dr3y/BioPick/images/colony_picker.png

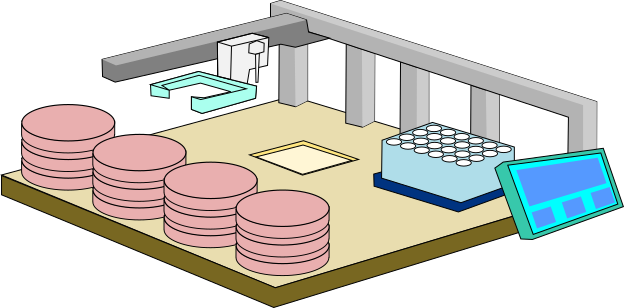
images/colony_picker.png
