dr3y/BioPick/images/IMG_20200820_125340495.jpg

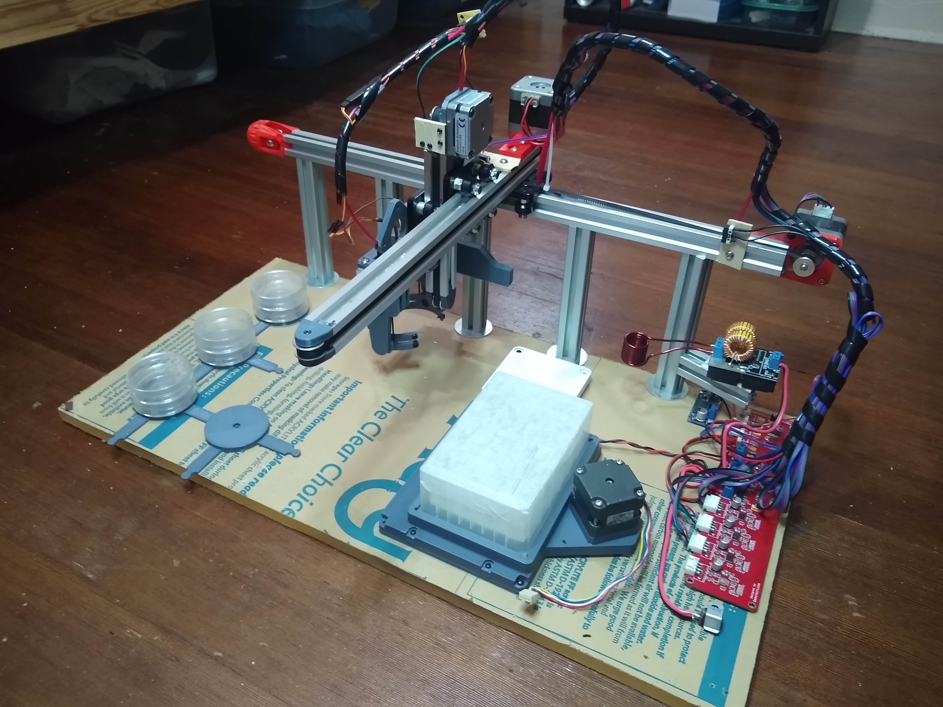
images/IMG_20200820_125340495.jpg
