dr3y/BioPick/software/raspberry_pi/pictures/A1_calib.png

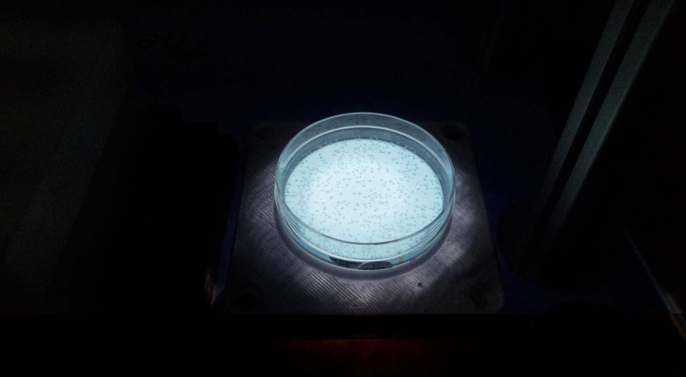
software/raspberry_pi/pictures/A1_calib.png
