dr3y/BioPick/physical/stl/plate_shaker/driver_pulley.stl

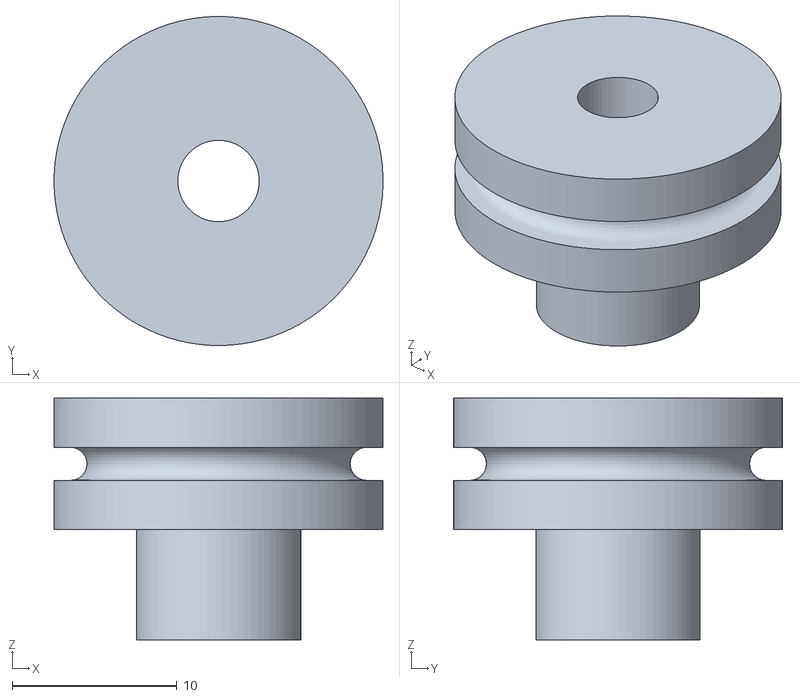
[picture p21: CAD file, 2020-08-20]
physical/stl/plate_shaker/driver_pulley.stl
20.0 x 20.0 x 14.7
