dr3y/BioPick/physical/stl/frame/idle_holder2.stl

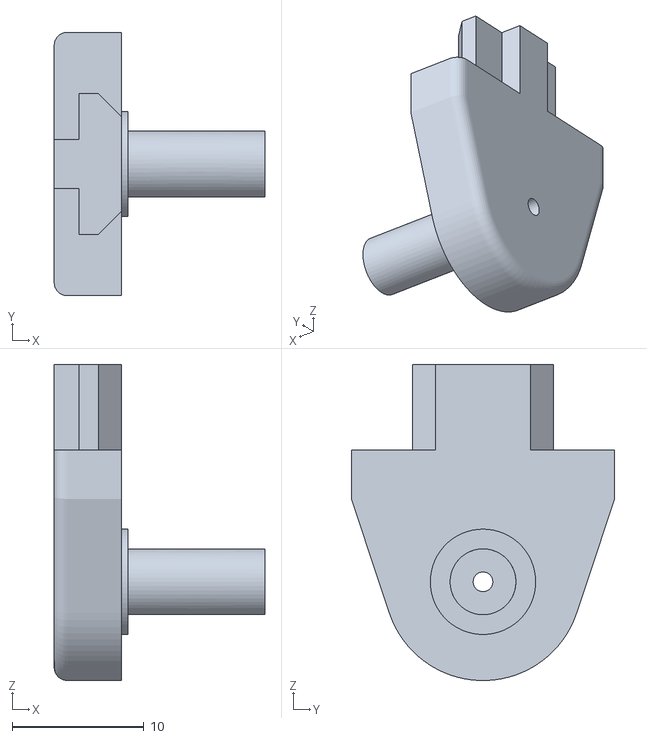
[picture p22: CAD file, 2020-08-20]
physical/stl/frame/idle_holder2.stl
16.0 x 20.0 x 24.0
