dr3y/BioPick/physical/stl/gripper/outershaft_bigger.stl

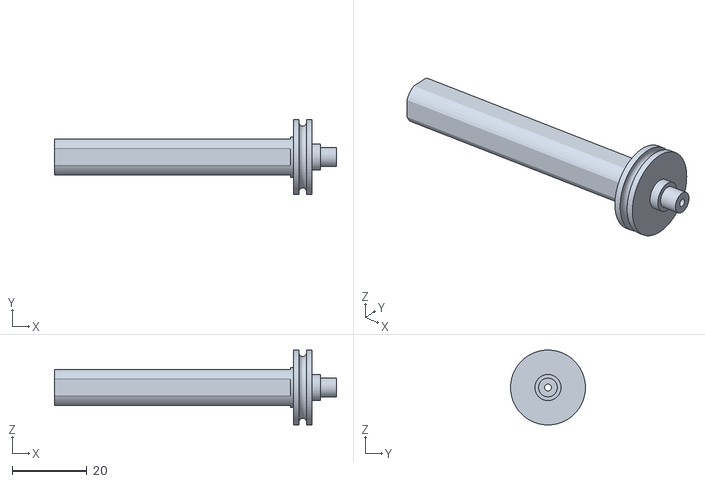
[picture p23: CAD file, 2020-08-20]
physical/stl/gripper/outershaft_bigger.stl
75.2 x 20.0 x 20.0
