dr3y/BioPick/physical/stl/plate_shaker/top_stator.stl

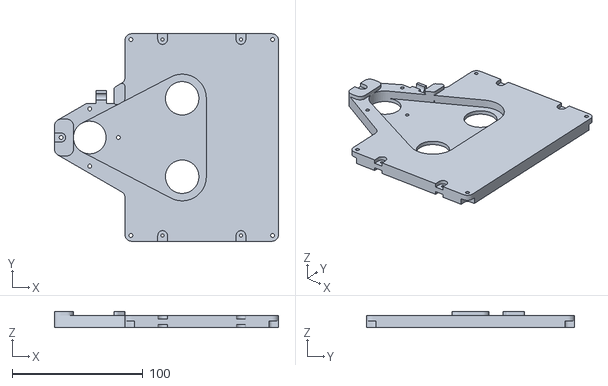
[picture p24: CAD file, 2020-08-20]
physical/stl/plate_shaker/top_stator.stl
171.5 x 159.0 x 12.5
