dr3y/BioPick/physical/stl/frame/motorholder.stl

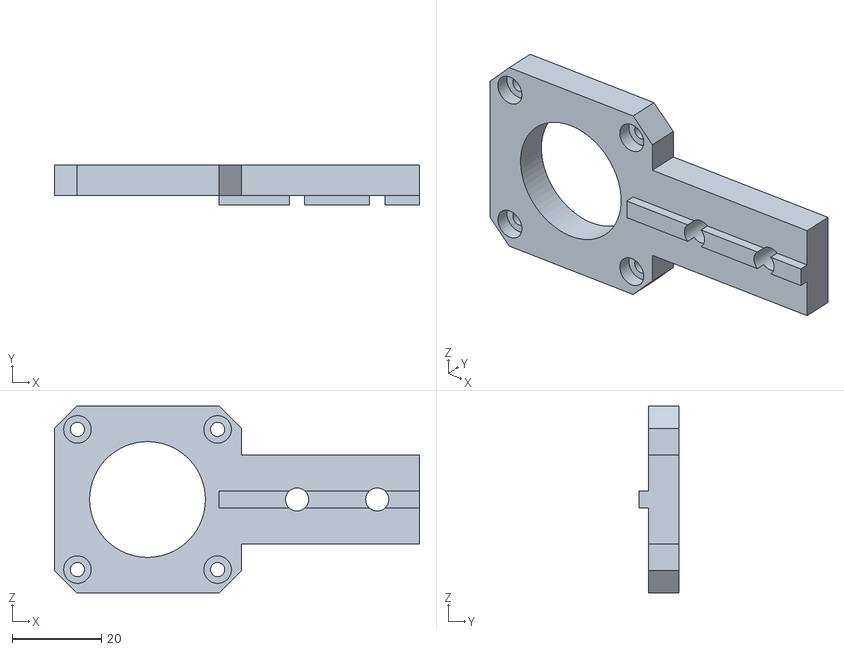
[picture p25: CAD file, 2020-08-20]
physical/stl/frame/motorholder.stl
82.0 x 9.00 x 42.0
