dr3y/BioPick/physical/stl/gripper/bearing cover.stl

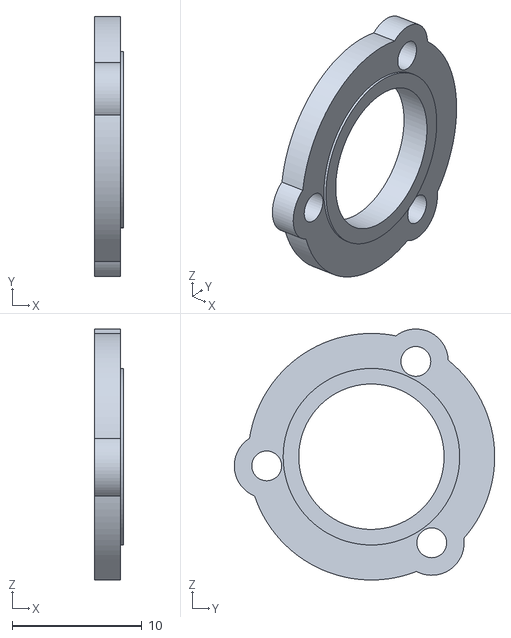
[picture p26: CAD file, 2020-08-20]
physical/stl/gripper/bearing cover.stl
2.20 x 20.1 x 19.3
