dr3y/BioPick/physical/stl/plate_shaker/rotor_pulley.stl

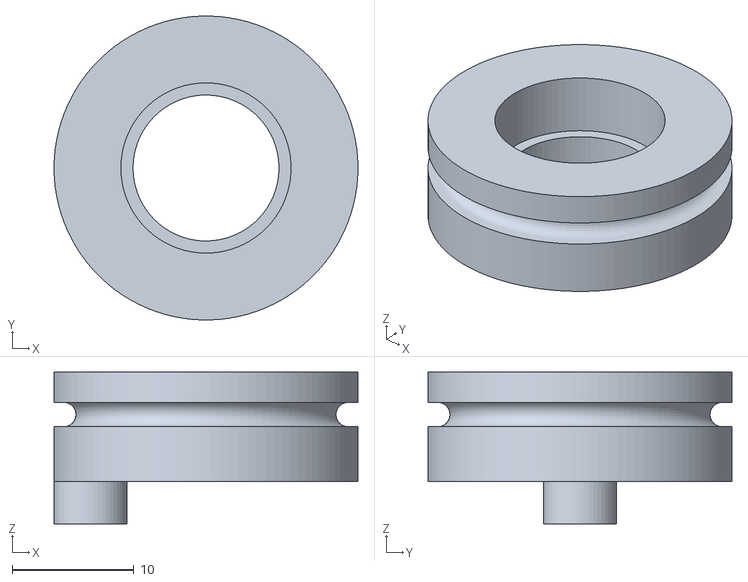
[picture p27: CAD file, 2020-08-20]
physical/stl/plate_shaker/rotor_pulley.stl
25.0 x 25.0 x 12.5
