dr3y/BioPick/physical/stl/frame/gripmount.stl

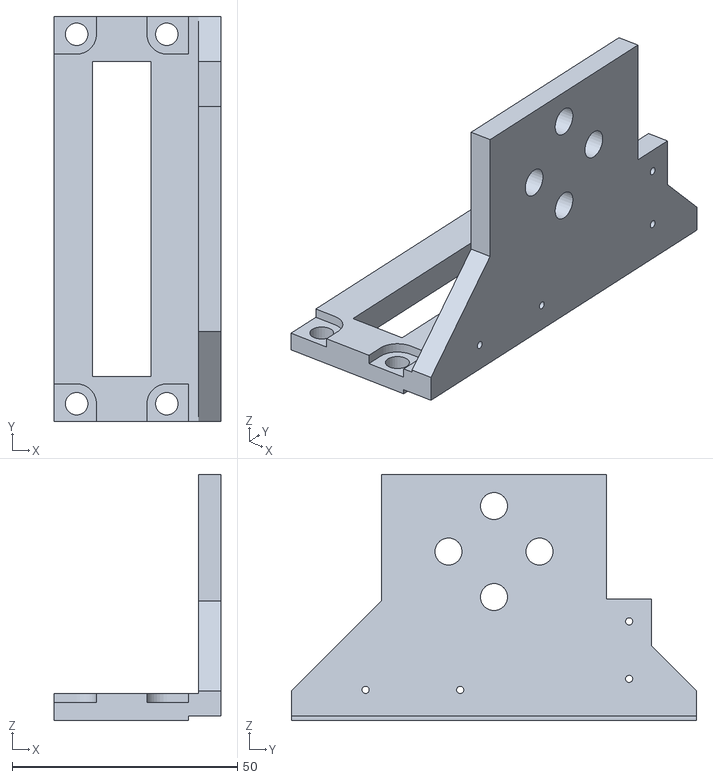
[picture p28: CAD file, 2020-08-20]
physical/stl/frame/gripmount.stl
37.0 x 90.0 x 54.6
