dr3y/BioPick/physical/stl/frame/y_clamp.stl

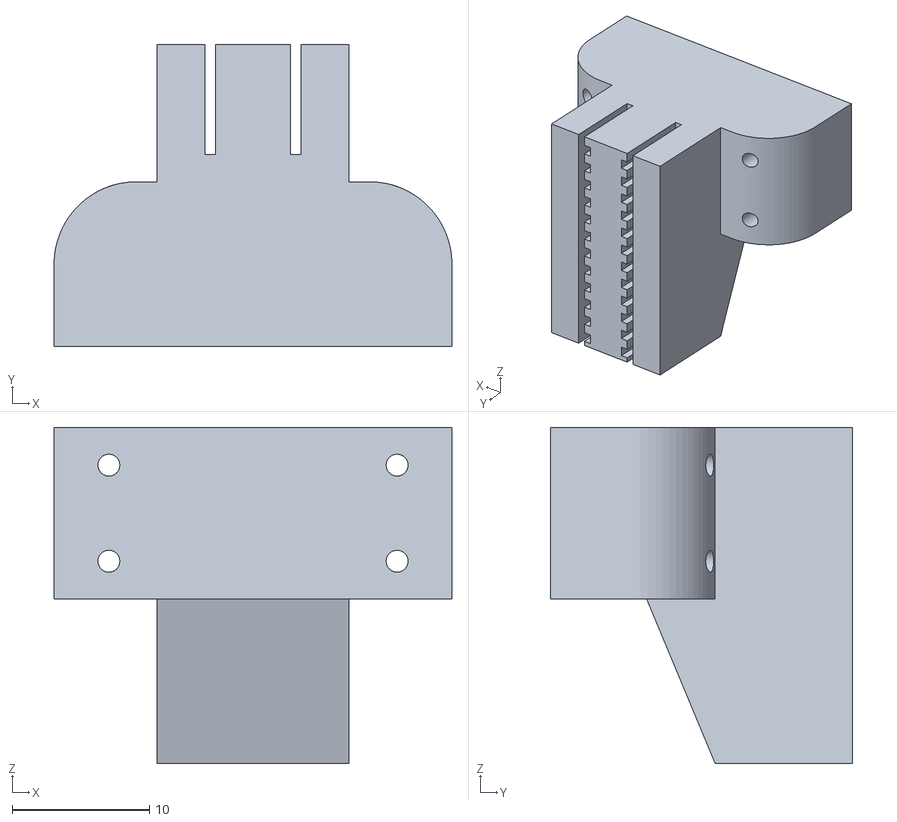
[picture p30: CAD file, 2020-08-20]
physical/stl/frame/y_clamp.stl
29.0 x 22.0 x 24.5
