dr3y/BioPick/physical/stl/gripper/largebevelgear.stl

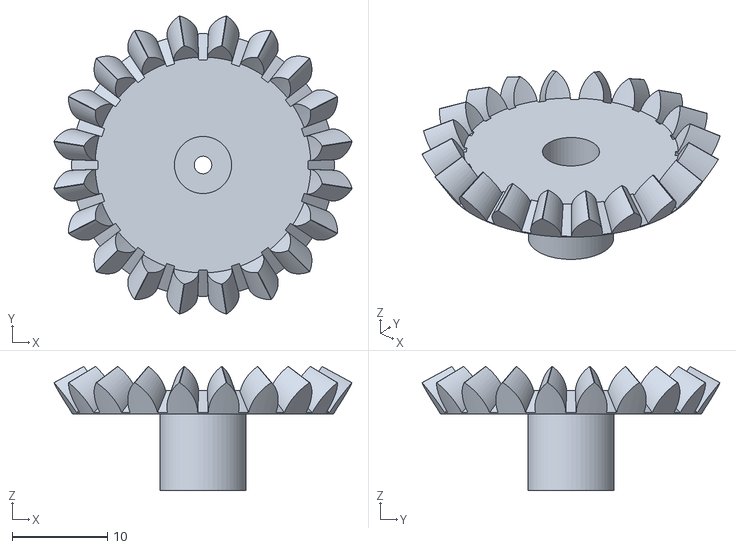
[picture p31: CAD file, 2020-08-20]
physical/stl/gripper/largebevelgear.stl
31.3 x 31.3 x 13.0
