dr3y/BioPick/physical/stl/plate_shaker/motor_spacer.stl

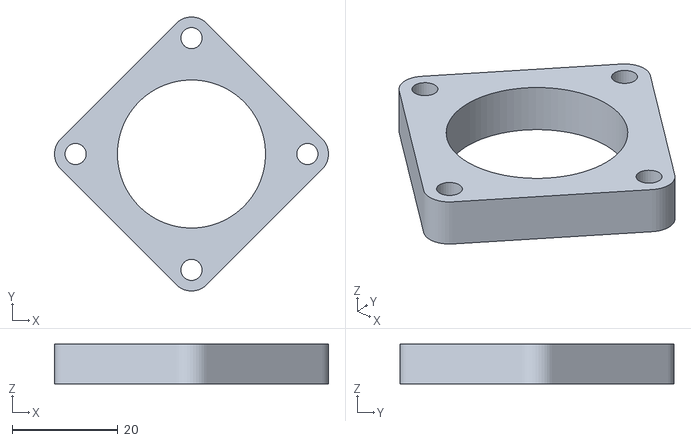
[picture p32: CAD file, 2020-08-20]
physical/stl/plate_shaker/motor_spacer.stl
51.8 x 51.8 x 7.50
