dr3y/BioPick/physical/stl/gripper/hand.stl

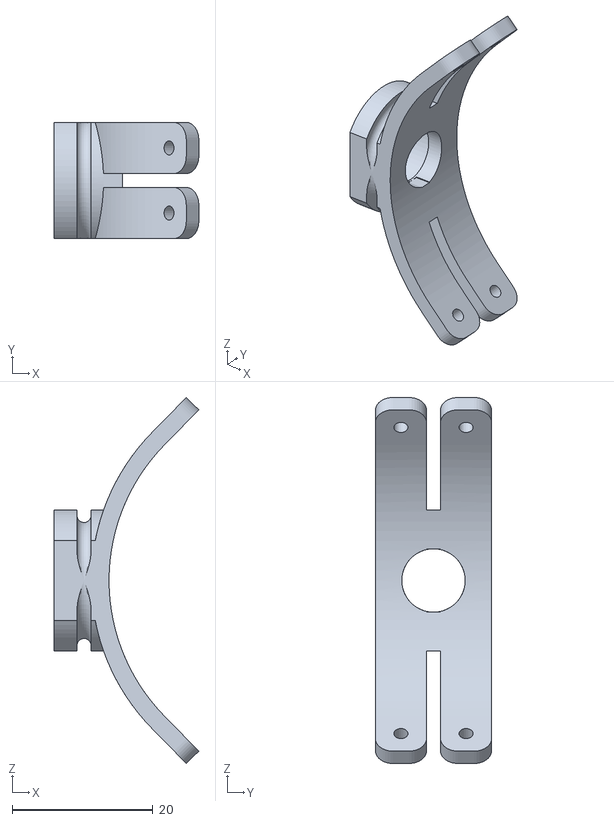
[picture p33: CAD file, 2020-08-20]
physical/stl/gripper/hand.stl
20.6 x 16.5 x 52.0
