dr3y/BioPick/physical/stl/gripper/bevelmount_biggerhole.stl

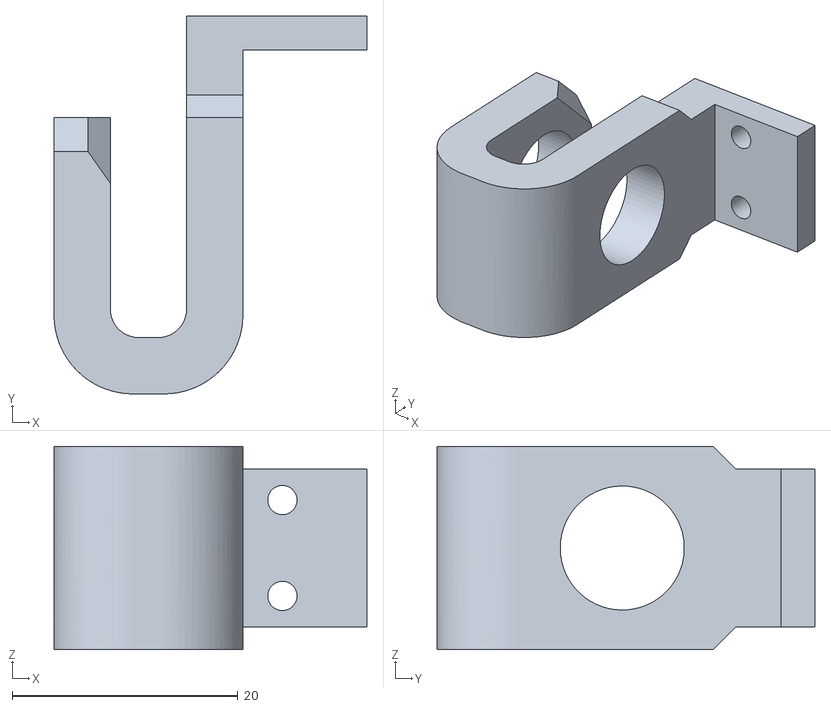
[picture p34: CAD file, 2020-08-20]
physical/stl/gripper/bevelmount_biggerhole.stl
27.8 x 33.5 x 18.0
