dr3y/BioPick/physical/stl/gripper/arm.stl

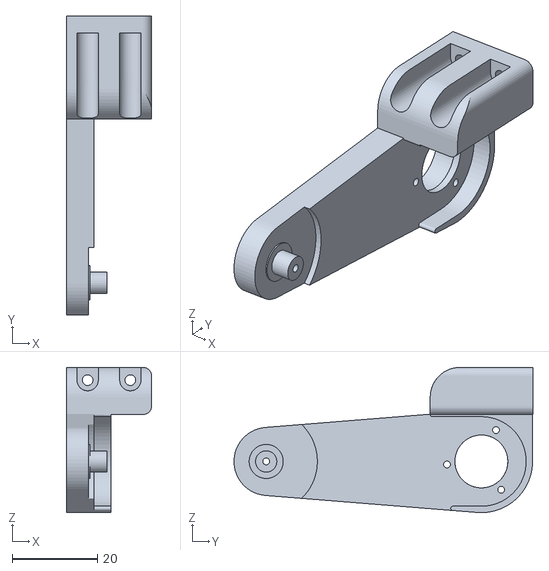
[picture p35: CAD file, 2020-08-20]
physical/stl/gripper/arm.stl
20.0 x 70.1 x 34.0
