dr3y/BioPick/physical/stl/gripper/rack.stl

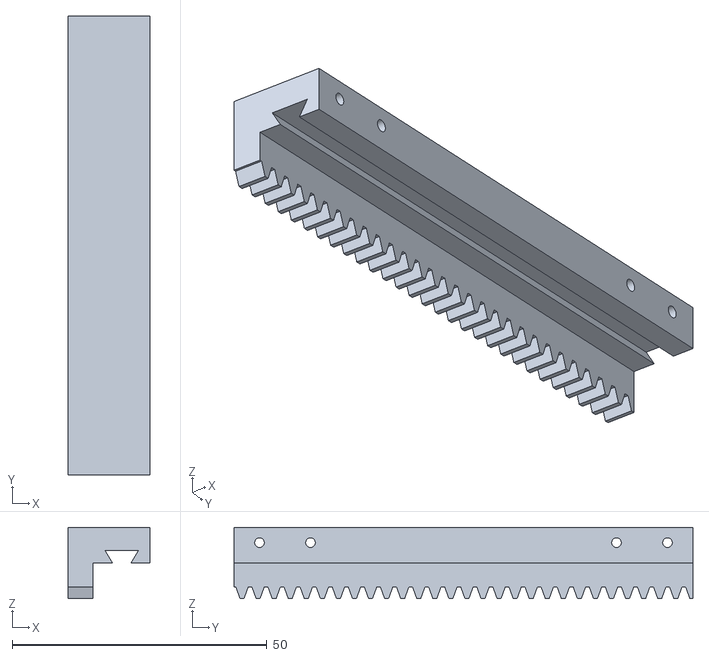
[picture p36: CAD file, 2020-08-20]
physical/stl/gripper/rack.stl
16.0 x 90.0 x 14.0
