dr3y/BioPick/software/raspberry_pi/calibration/aruco1.png

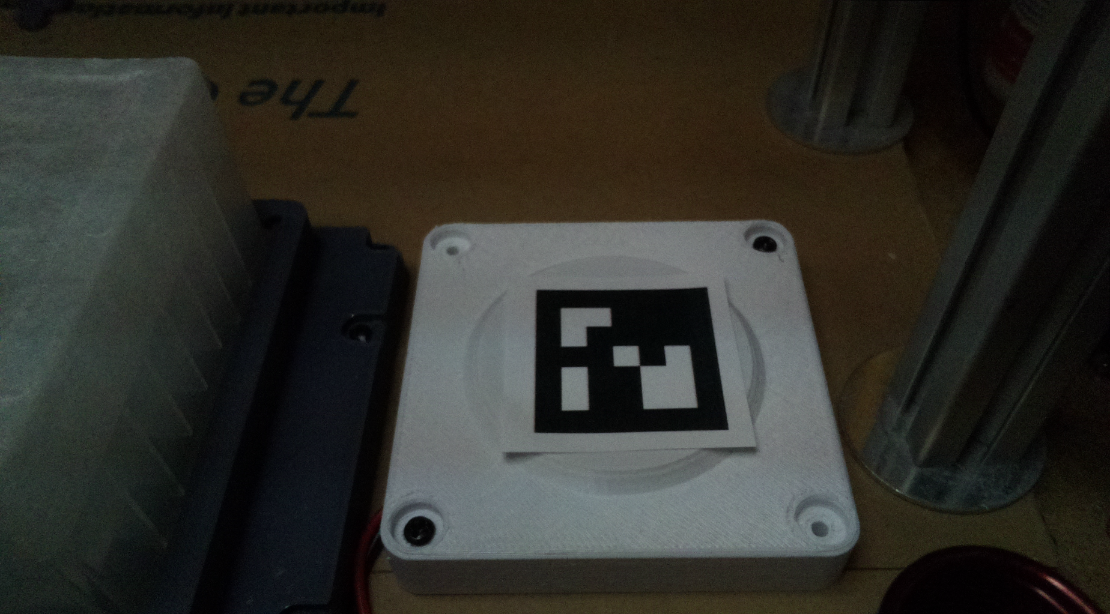
software/raspberry_pi/calibration/aruco1.png
