dr3y/BioPick/software/raspberry_pi/calibration/aruco2.png

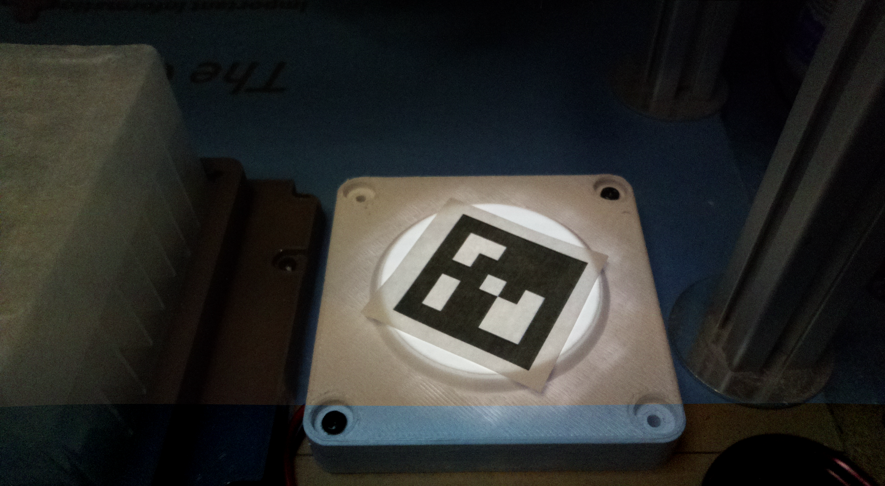
software/raspberry_pi/calibration/aruco2.png
