dr3y/BioPick/software/raspberry_pi/calibration/calib4.png

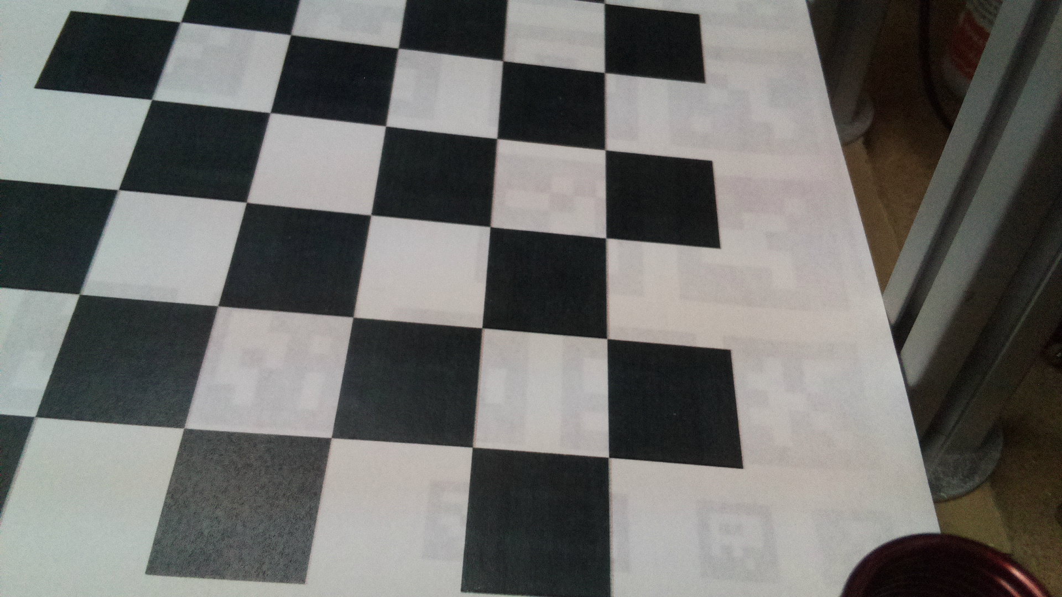
software/raspberry_pi/calibration/calib4.png
