dr3y/BioPick/software/raspberry_pi/calibration/calib5.png

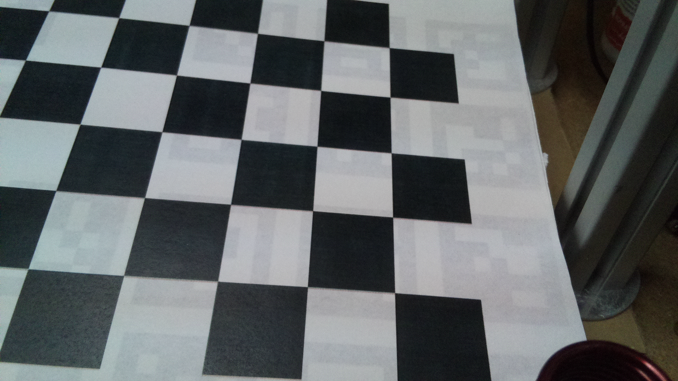
software/raspberry_pi/calibration/calib5.png
