dr3y/BioPick/software/raspberry_pi/calibration/calib7.png

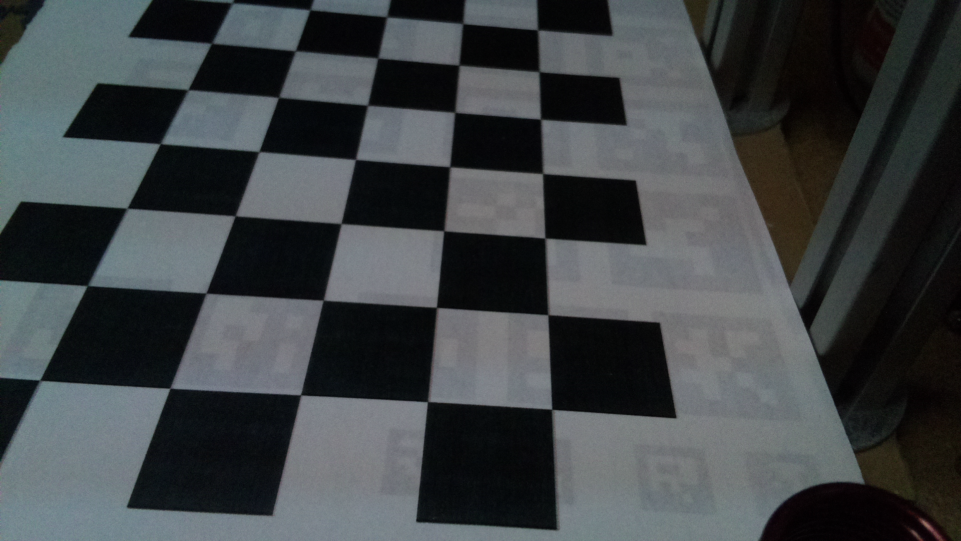
software/raspberry_pi/calibration/calib7.png
